g4eml/OpenMD9600_Remote_Head/Pics/IMG2.jpg

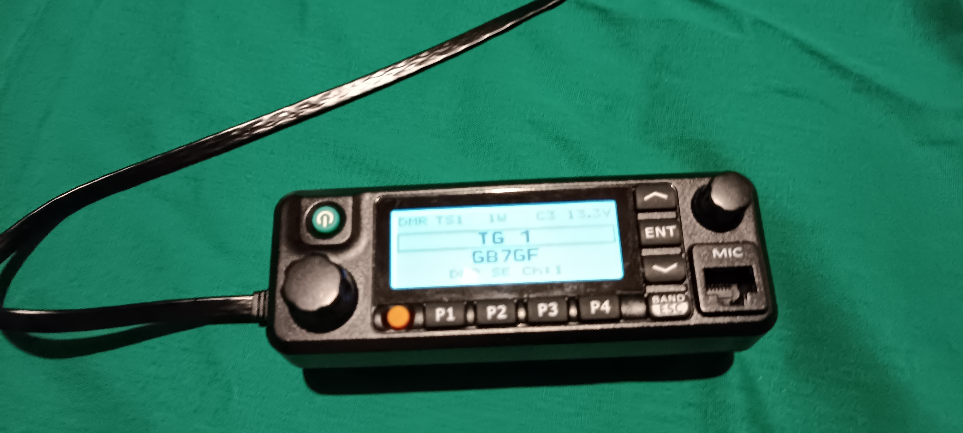
Pics/IMG2.jpg
