g4eml/OpenMD9600_Remote_Head/Pics/IMG3.jpg

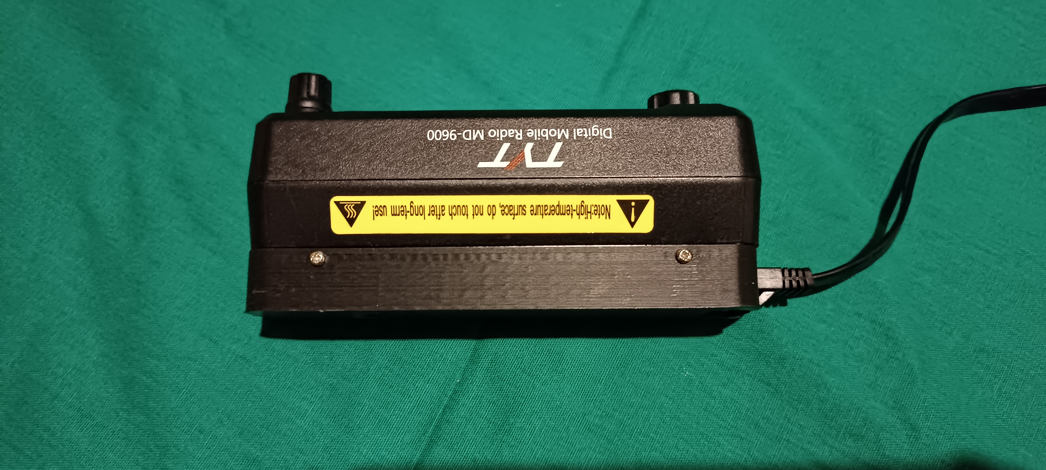
Pics/IMG3.jpg
