g4eml/OpenMD9600_Remote_Head/Pics/IMG4.jpg

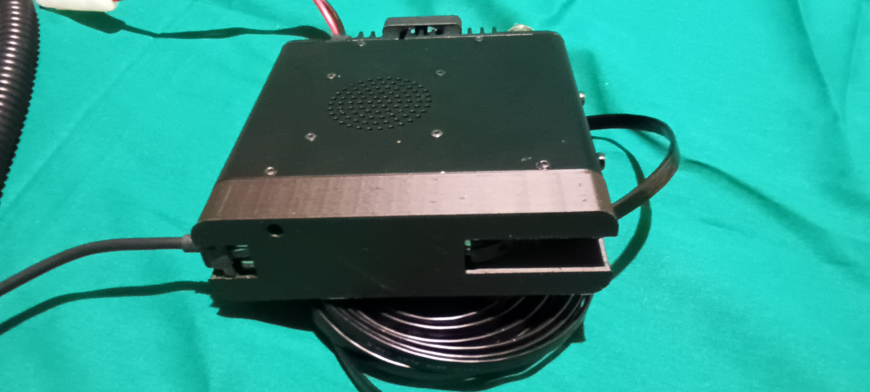
Pics/IMG4.jpg
