g4eml/OpenMD9600_Remote_Head/Pics/IMG5.jpg

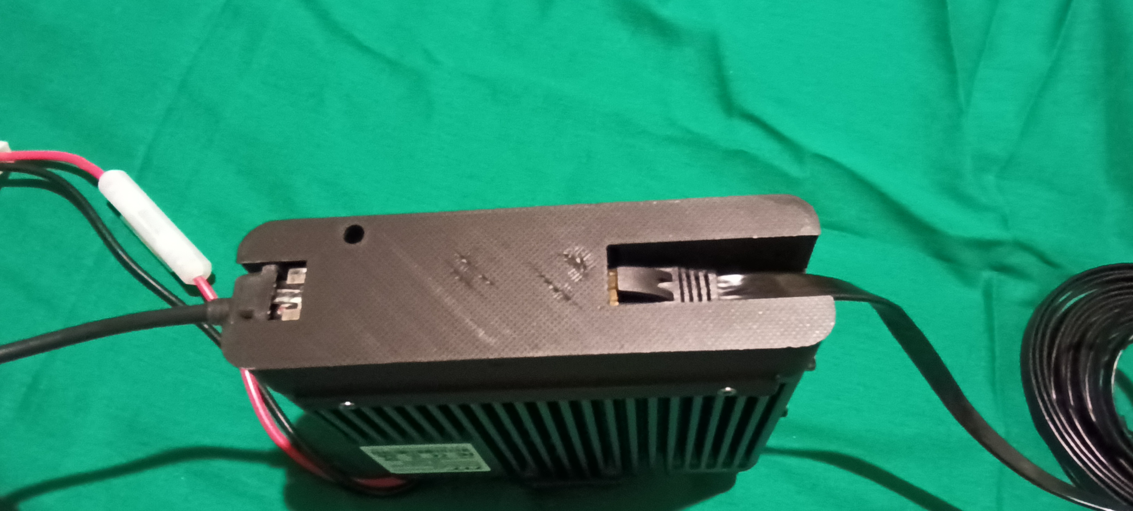
Pics/IMG5.jpg
