g4eml/OpenMD9600_Remote_Head/Pics/IMG6.jpg

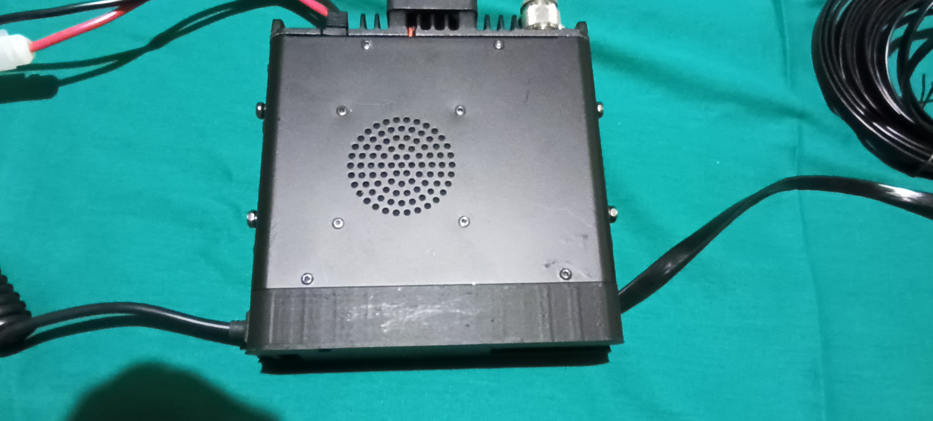
Pics/IMG6.jpg
